andreas-di/jupyter/content/bilder/bogenlaenge_bis_x.png

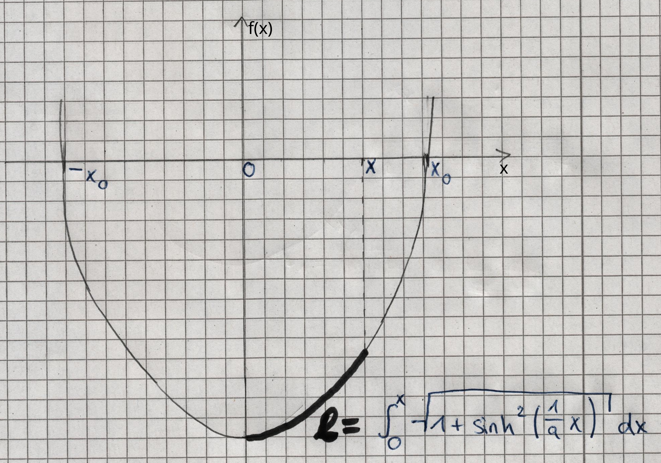
content/bilder/bogenlaenge_bis_x.png
