andreas-di/jupyter/content/bilder/drehmatrix.png

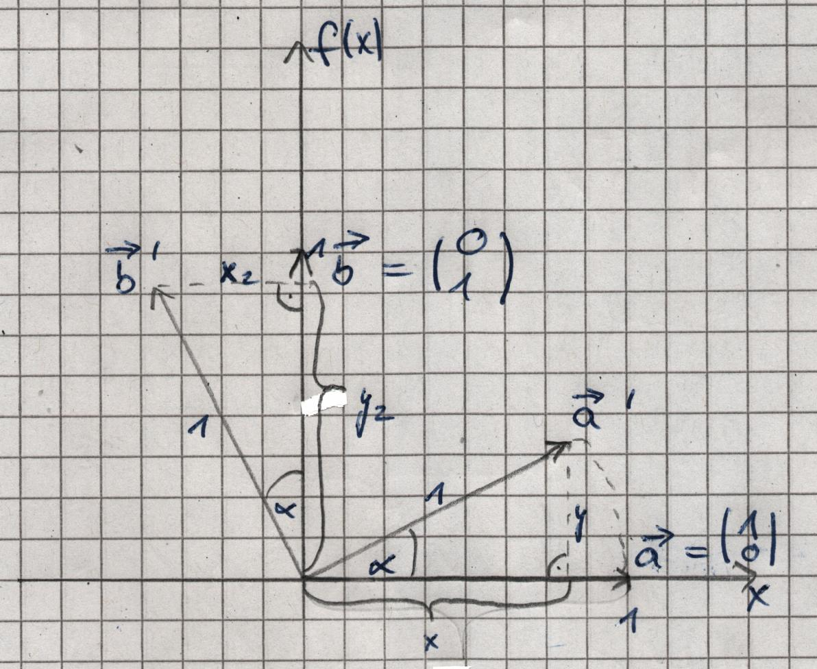
content/bilder/drehmatrix.png
