andreas-di/jupyter/content/bilder/Laebgebelement.png

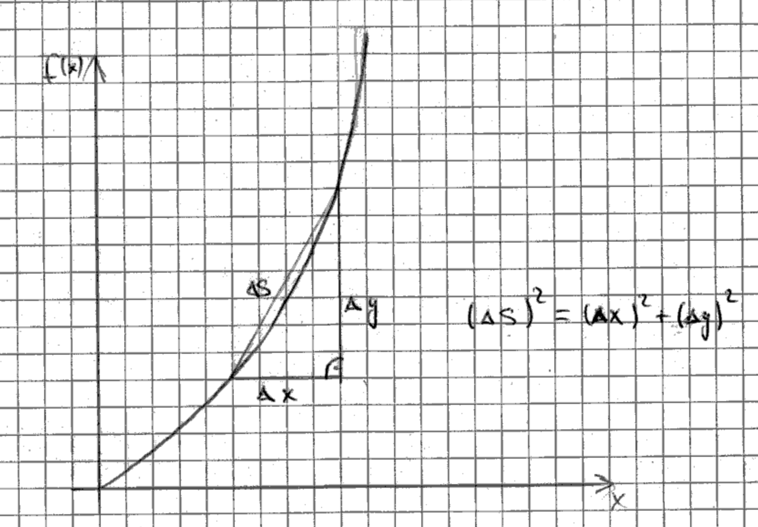
content/bilder/Laebgebelement.png
