andreas-di/jupyter/content/bilder/plot_mit_stuecken.png

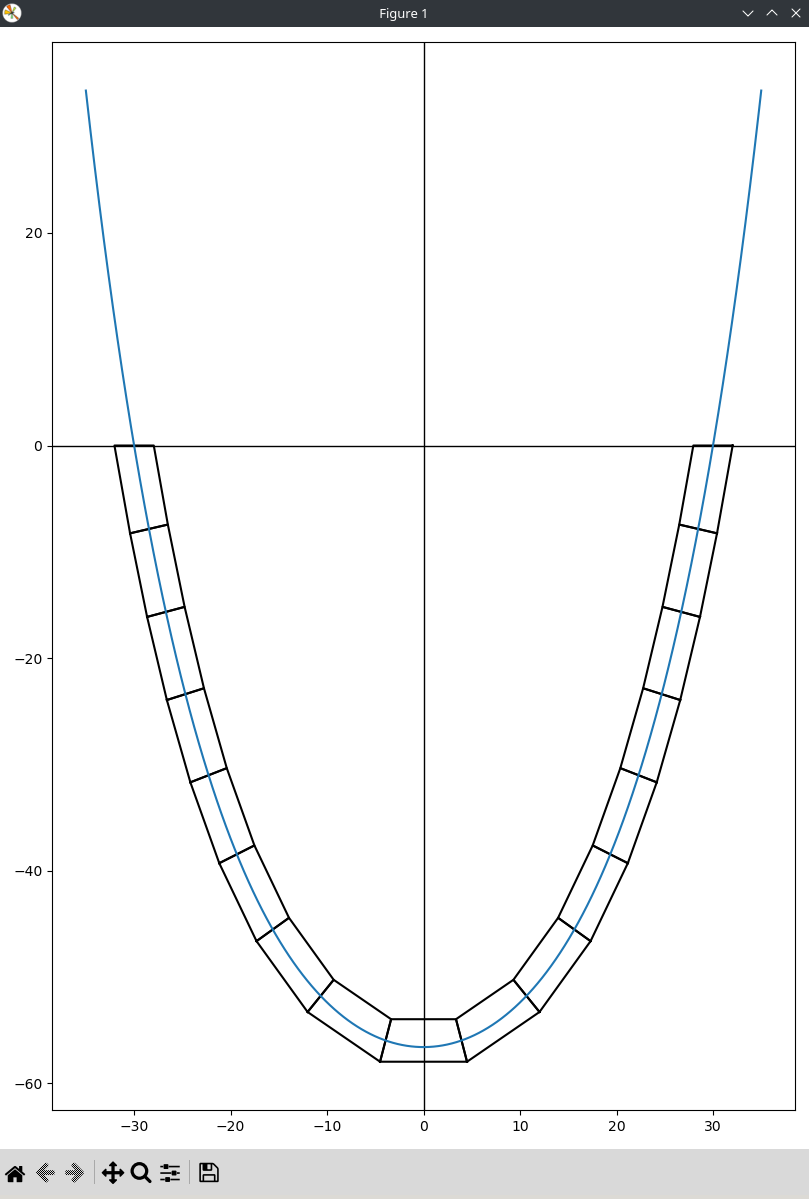
content/bilder/plot_mit_stuecken.png
