andreas-di/jupyter/content/bilder/Python_Ausgabe_Kettenlinie.png

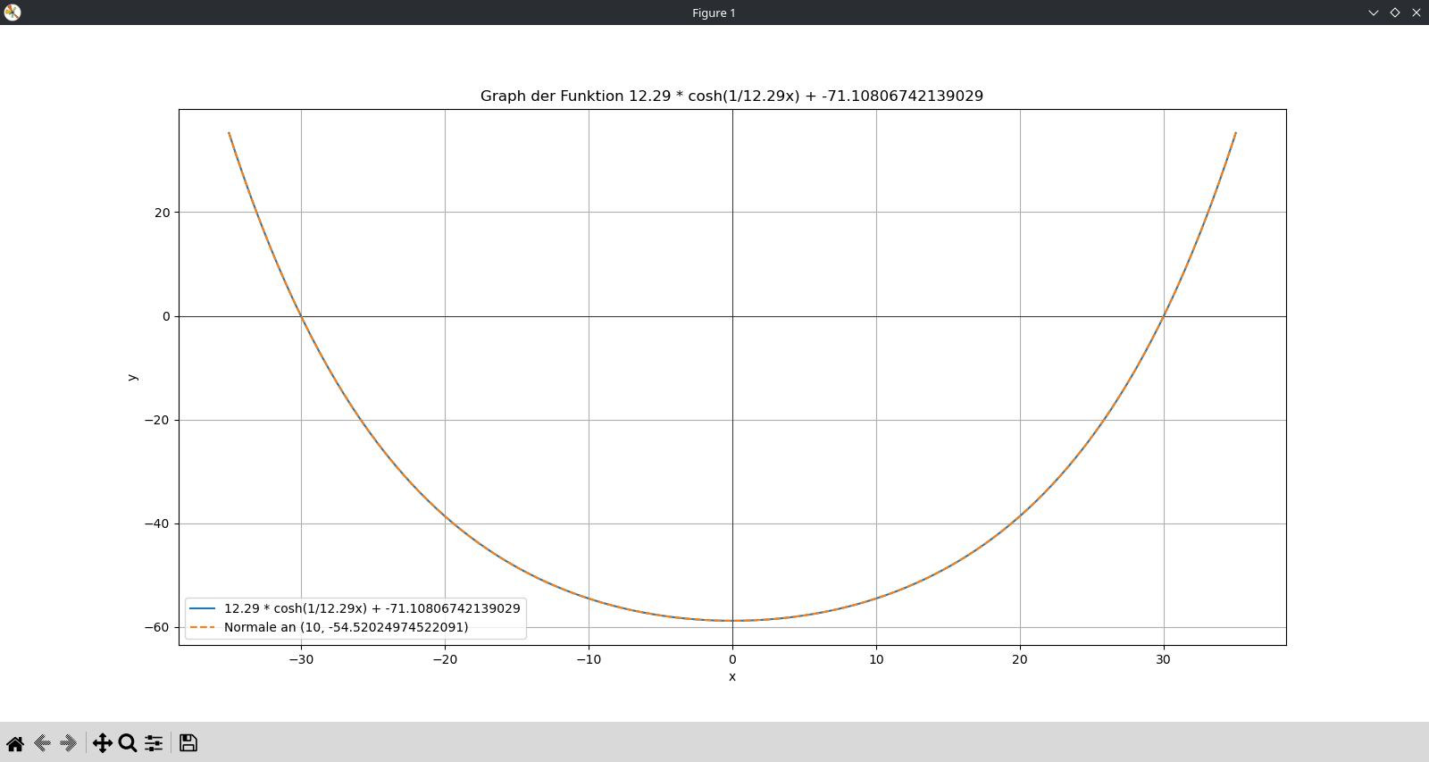
content/bilder/Python_Ausgabe_Kettenlinie.png
