andreas-di/jupyter/content/bilder/schneidewinkel.png

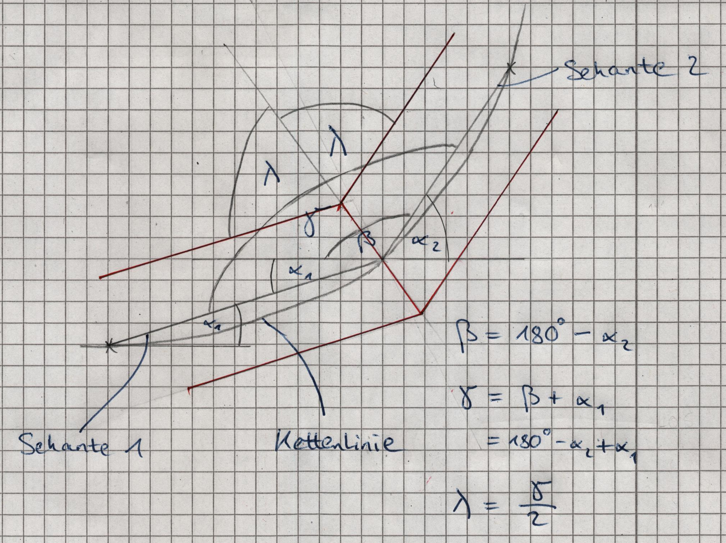
content/bilder/schneidewinkel.png
