andreas-di/jupyter/content/bilder/vektoren_r3.png

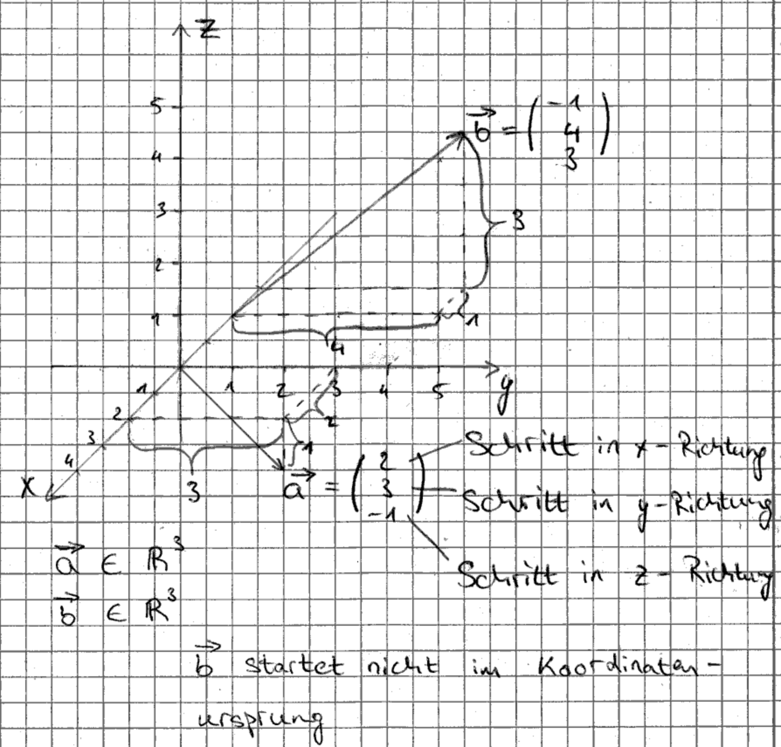
content/bilder/vektoren_r3.png
